Taro-Hayashi/Cannonball-LL/img/drive.jpg

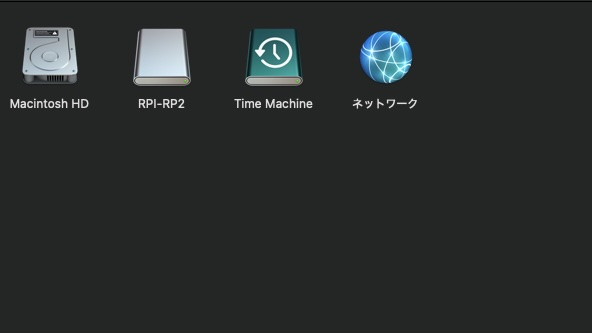
img/drive.jpg
