Taro-Hayashi/Cannonball-LL/img/IMG_0543.png

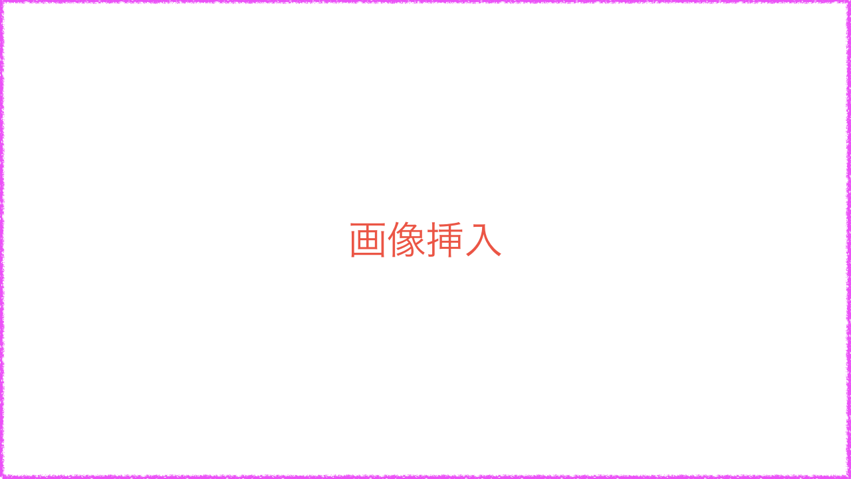
img/IMG_0543.png
