Taro-Hayashi/Cannonball-LL/img/IMG_0576.jpg

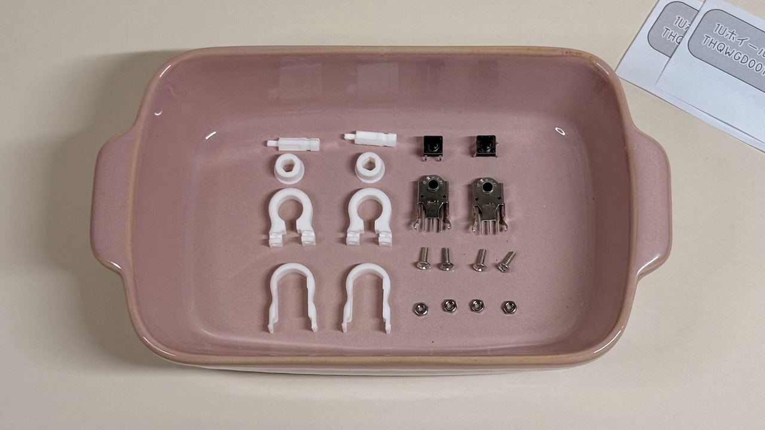
img/IMG_0576.jpg
