Taro-Hayashi/Cannonball-LL/img/IMG_0911.jpg

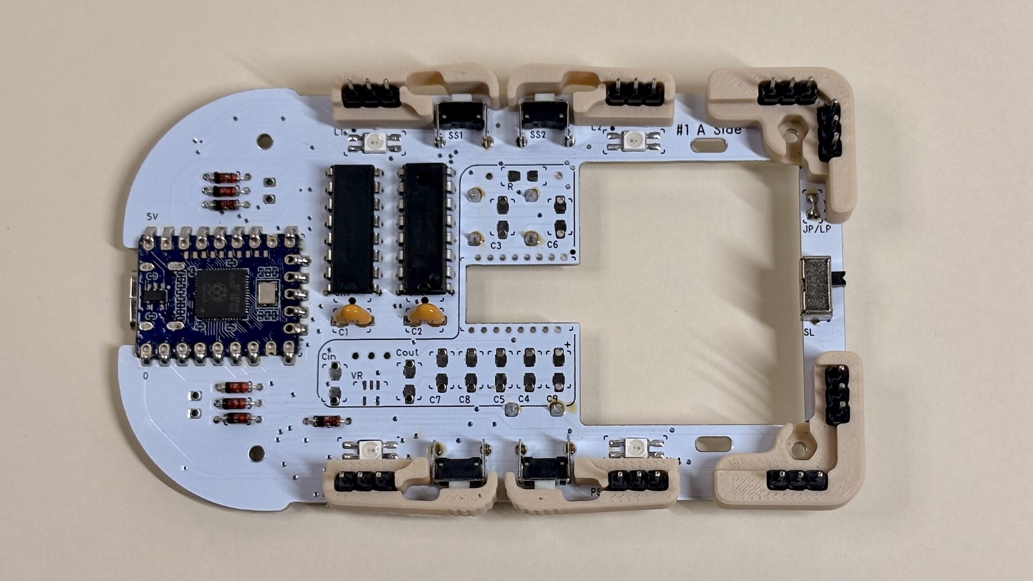
img/IMG_0911.jpg
