Taro-Hayashi/Cannonball-LL/img/IMG_1108.jpg

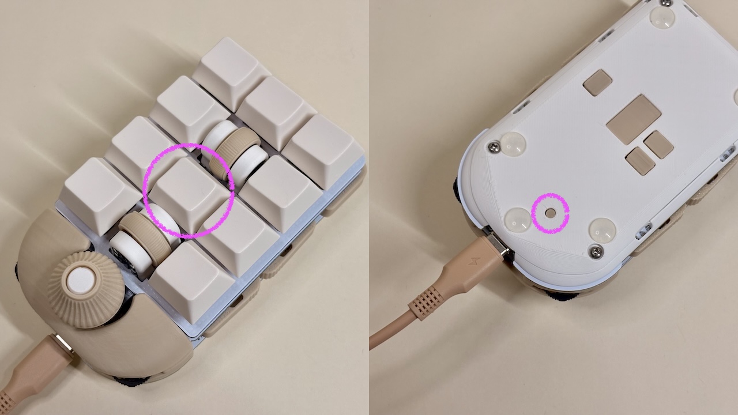
img/IMG_1108.jpg
