Taro-Hayashi/Cannonball-LL/img/IMG_1479.jpg

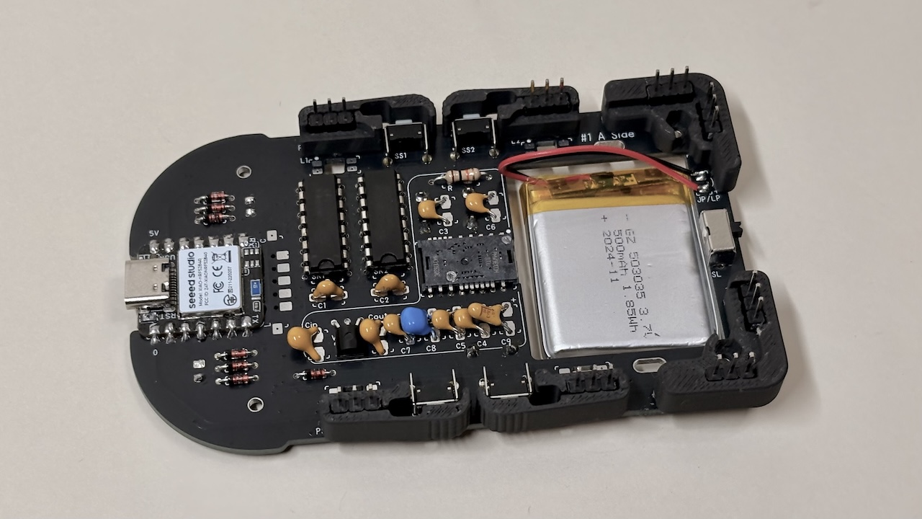
img/IMG_1479.jpg
