Taro-Hayashi/Cannonball-LL/img/optional.jpg

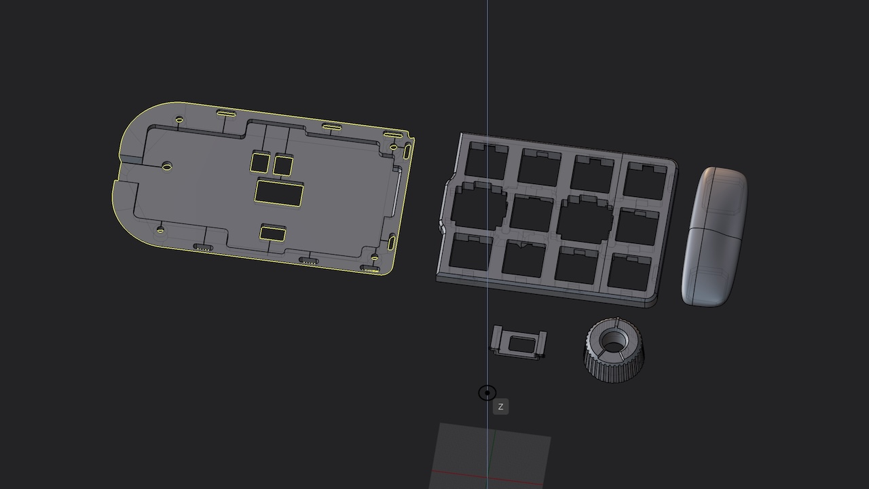
img/optional.jpg
