Taro-Hayashi/Cannonball-LL/stl/included/Bottom #1.stl

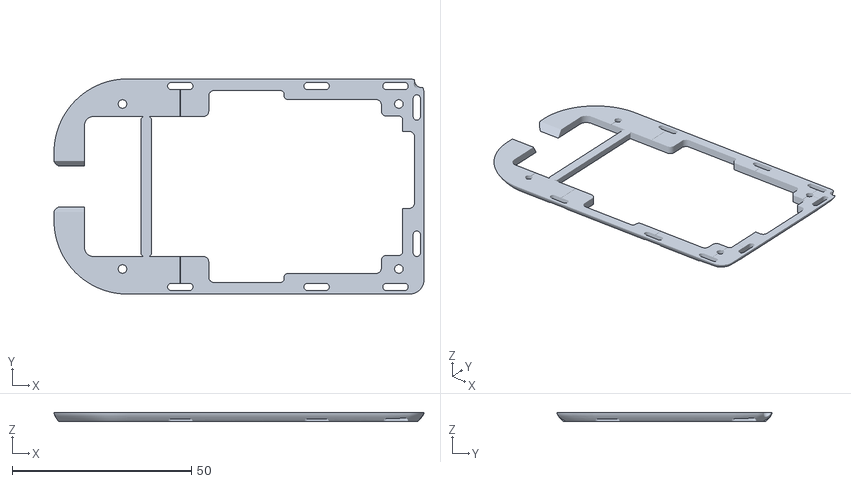
[picture p170: CAD file, 2025-04-05]
stl/included/Bottom #1.stl
103.2 x 60.0 x 2.50
