Taro-Hayashi/Cannonball-LL/stl/included/Blocker.stl

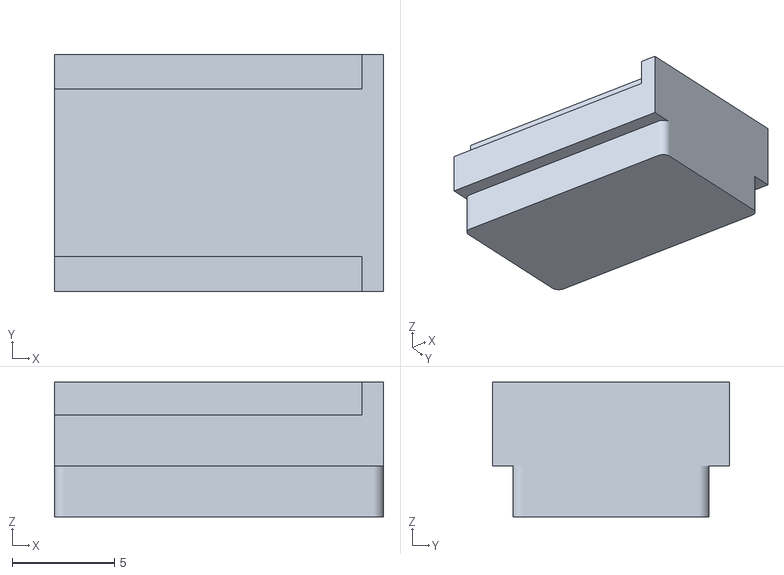
[picture p171: CAD file, 2025-04-05]
stl/included/Blocker.stl
16.1 x 11.6 x 6.60
