Taro-Hayashi/Cannonball-LL/stl/included/Side #9.stl

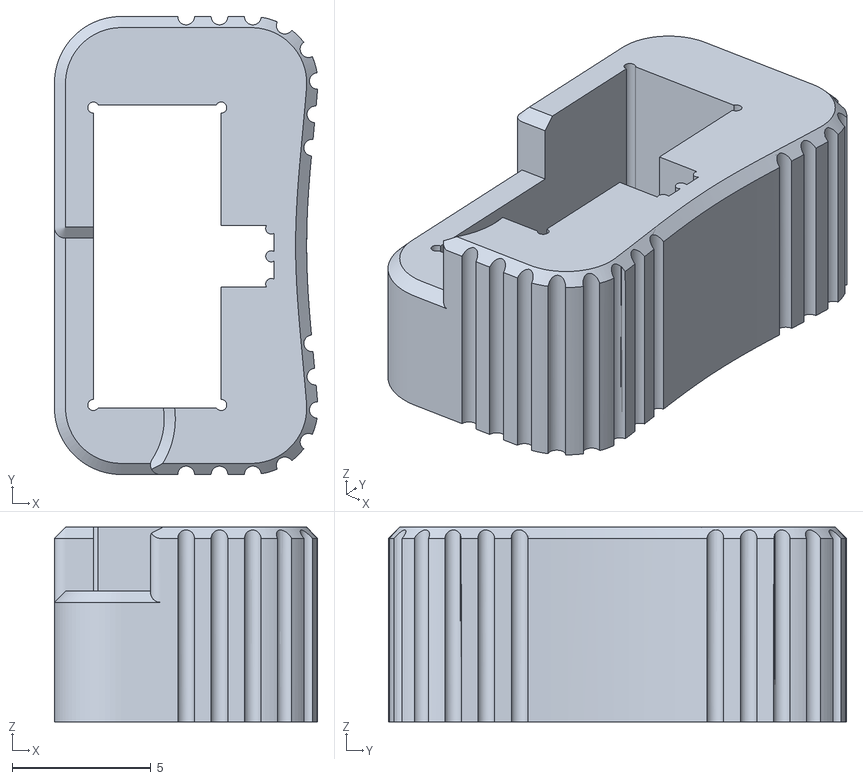
[picture p172: CAD file, 2025-04-05]
stl/included/Side #9.stl
9.47 x 16.5 x 7.00
