Taro-Hayashi/Cannonball-LL/stl/included/Reset Button.stl

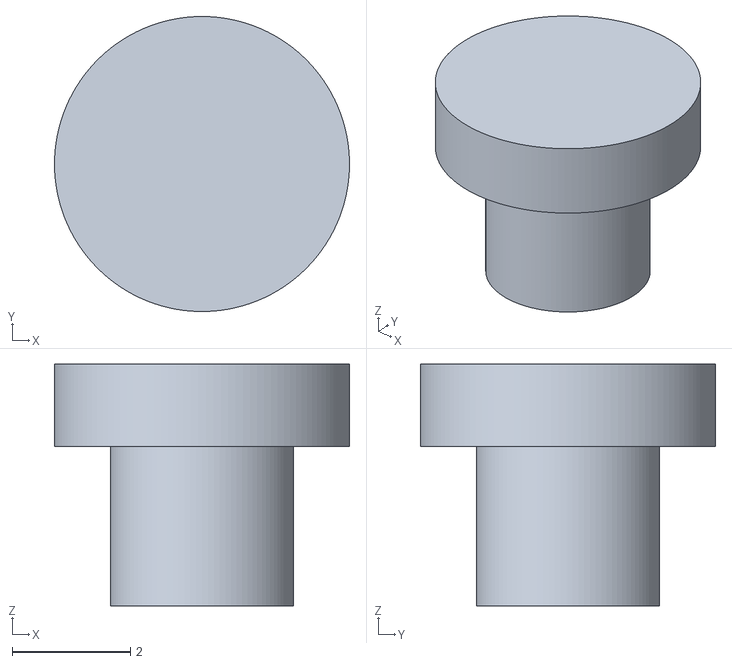
[picture p173: CAD file, 2025-04-05]
stl/included/Reset Button.stl
5.00 x 5.00 x 4.10
