Taro-Hayashi/Cannonball-LL/qmk_firmware/keyboards/cannonballll/halconf.h

// Copyright 2025 Hayashi (@w_vwbw)
// SPDX-License-Identifier: GPL-3.0-or-later

#pragma once
#define HAL_USE_ADC FALSE
#define HAL_USE_I2C FALSE
#define HAL_USE_SPI TRUE

#define SPI_USE_WAIT TRUE
#define SPI_SELECT_MODE SPI_SELECT_MODE_PAD
#define SERIAL_USB_BUFFERS_SIZE 256

#include_next <halconf.h>
